R3DPanda1/WirelessMotionSensor/include/main.h

#ifndef MAIN_H
#define MAIN_H

#include <Arduino.h>
#include <rendering.h>
#include <sensor.h>
#include <bluetooth.h>
#include <button.h>
#include <Wire.h>
#include "commons.h"
#include "sd_card.h"
//#include <utility/imumaths.h>
//#include <math.h>

#if !defined(CONFIG_BT_SPP_ENABLED)
#error Serial Bluetooth not available or not enabled. It is only available for the ESP32 chip.
#endif

#endif // MAIN_H
