R3DPanda1/WirelessMotionSensor/src/button.cpp

#include <button.h>

TaskHandle_t buttonTaskHandle = NULL;

void buttonTask(void *pvParameters)
{

    const int buttonPins[] = {REC_SW_PIN, BT_SW_PIN, MODE_SW_PIN, CLK_SYNC_SW_PIN};

    enum Buttons
    {
        None = 0,
        REC_SW = 1,
        BT_SW = 2,
        MODE_SW = 3,
        CLK_SYNC_SW = 4
    };

    int lastButtonStates[] = {HIGH, HIGH, HIGH, HIGH};
    long lastDebounceTimes[] = {0, 0, 0, 0};
    long debounceDelay = 100;

    int buttonPressed = None;

    // initialize buttons
    for (int i = 0; i < 4; i++)
    {
        pinMode(buttonPins[i], INPUT_PULLUP);
    }

    vTaskDelay(100 / portTICK_PERIOD_MS); // buttons can

    // loop
    for (;;)
    {
        for (int i = 0; i < 4; i++)
        {
            int buttonState = digitalRead(buttonPins[i]);

            // check for state change from HIGH to LOW
            if (buttonState == LOW && lastButtonStates[i] == HIGH && millis() - lastDebounceTimes[i] > debounceDelay)
            {
                // button state changed from HIGH to LOW
                lastDebounceTimes[i] = millis();

                buttonPressed = i + 1;
                vTaskDelay(200 / portTICK_PERIOD_MS);
            }

            lastButtonStates[i] = buttonState;
        }

        switch (buttonPressed)
        {
        case REC_SW:
            if (currentSdState == CONNECTED)
            {
                if (currentRecordingMode == IDLE)
                {
                    displayNotification("Recording...");
                    currentRecordingMode = CREATE_FILE;
                }
                else
                {
                    displayNotification("Recording stopped");
                    currentRecordingMode = IDLE;
                }
            }
            else if (currentSdState == FAILED)
            {
                displayNotification("Can't connect SD");
            }
            else
            {
                displayNotification("No SD connected");
            }
            break;
        case BT_SW:
            switch (currentBluetoothMode)
            {
            case MODE_DISCONNECTED:
                currentBluetoothMode = MODE_CONNECT;
                displayNotification("Connecting...");
                break;
            case MODE_CONNECTED:
                currentBluetoothMode = MODE_DISCONNECT;
                break;
            case MODE_CONNECTING:
                displayNotification("Still connecting");
                break;
            }
            break;
        case MODE_SW:
            if (btRole == SLAVE && currentBluetoothMode == MODE_CONNECTED)
            {
                displayNotification("Not BT master");
            }
            else
            {
                switch (currentOperationMode)
                {
                case MODE_FUSION:
                    currentOperationMode = MODE_TEMP;
                    displayNotification("Temperature");
                    break;
                case MODE_TEMP:
                    currentOperationMode = MODE_LEVEL;
                    displayNotification("Spirit Level");
                    break;
                case MODE_LEVEL:
                    currentOperationMode = MODE_RAW;
                    displayNotification("Raw");
                    break;
                case MODE_RAW:
                    currentOperationMode = MODE_FUSION;
                    displayNotification("Fusion");
                    break;
                }
            }
            break;
        case CLK_SYNC_SW:
            if (currentBluetoothMode == MODE_CONNECTED)
            {
                if (btRole == MASTER)
                {
                    if (currentOperationMode != MODE_CLK_SYNC)
                    {
                        currentSyncMode = MODE_SYNC_START;
                        currentOperationMode = MODE_CLK_SYNC;
                    }
                }
                else
                {
                    displayNotification("Not BT master");
                }
            }
            else
            {
                displayNotification("No BT connection");
            }

            break;
        default:
            // no button pressed
            break;
        }
        buttonPressed = 0;

        // Yield to other tasks
        vTaskDelay(10 / portTICK_PERIOD_MS);
    }
}
